arnebech/benjamins-traffic-system/pcb/Benjamins-Light-System-2.png

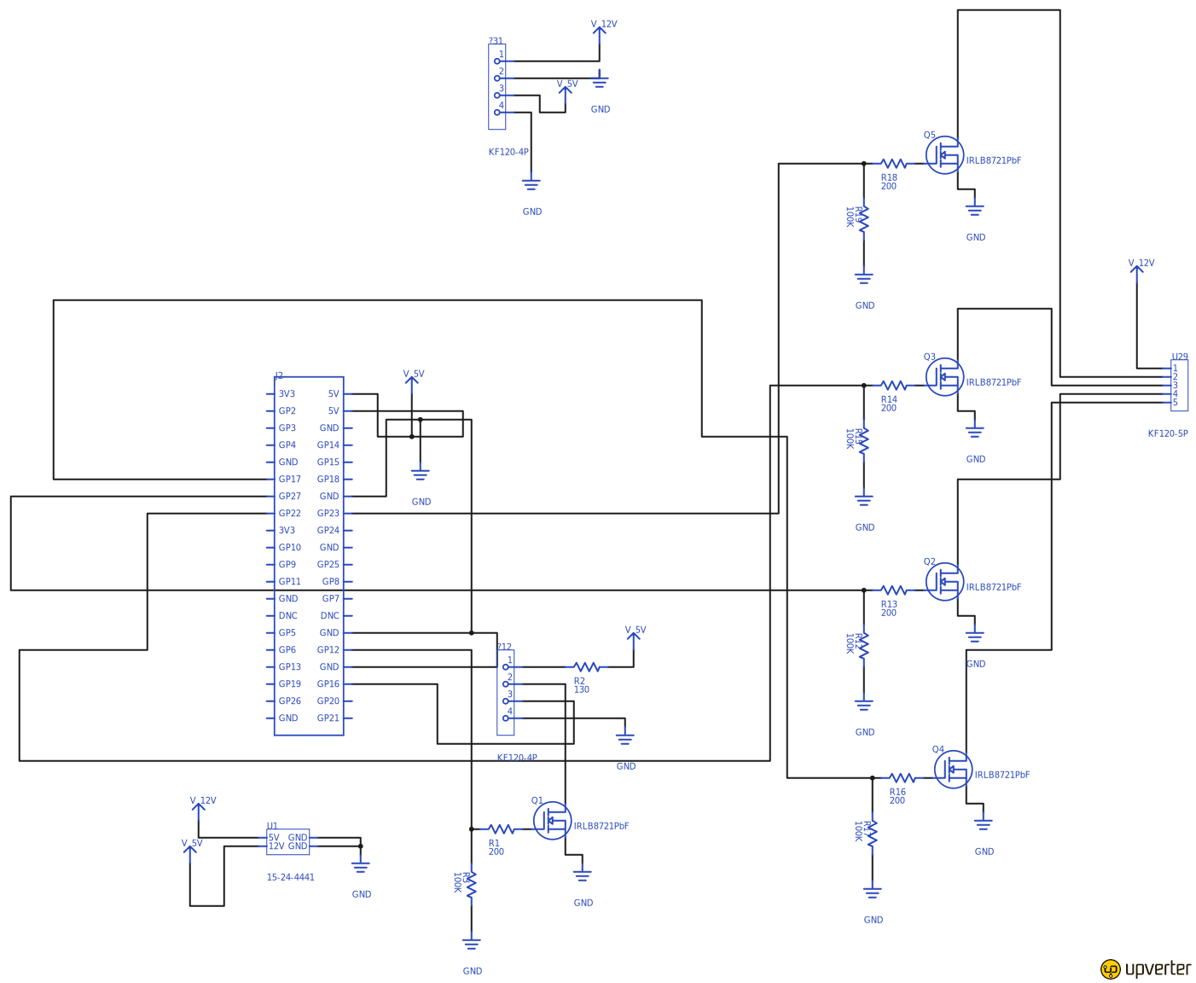
pcb/Benjamins-Light-System-2.png
